Salamandar/StrangerFamily/pyStranger/database.py

#!/bin/env python3
import os
from pathlib import Path

import random
import yaml

class Sentence(object):
    def __init__(self, text, speed):
        self.text = text
        self.speed= speed

    def __repr__(self):
        return '\'' + self.text + '\''

    def __str__(self):
        return self.text


class StrangerDatabase():
    def __init__(self):
        super(StrangerDatabase, self).__init__()
        self.persistentFile = Path(os.path.dirname(__file__)+'/stranger_strings.yaml')
        self.temporaryFile  = Path(os.path.dirname(__file__)+'/stranger_strings_temp.txt')

        self.sentences      = []
        self.sentences_temp = []
        self.should_echo_last_temp = False

        self.loadPersistent()
        self.loadTemp()

    def loadPersistent(self):
        self.sentences      = self.loadFile(self.persistentFile)
    def loadTemp(self):
        self.sentences_temp = self.loadFile(self.temporaryFile)

    def loadFile(self, path):
        if not path.exists():
            return []

        with path.open() as stream:
            try:
                data = yaml.load(stream)
                return [ Sentence(d['text'], d['speed']) for d in data['sentences'] ]
            except yaml.YAMLError as exc:
                print(exc)

    def saveToTemp(self, string):
        if not os.path.isfile(str(self.temporaryFile)):
            with open(str(self.temporaryFile), 'a') as tempFile:
                tempFile.write('sentences:\n')

        with open(str(self.temporaryFile), 'a') as tempFile:
            tempFile.write('  - text: \'' + string + '\'\n')
            tempFile.write('    speed: 1\n')


    def addSentence(self, string):
        self.sentences_temp += [ Sentence(string, 1) ]
        self.should_echo_last_temp = True
        self.saveToTemp(string)


    def getRandSentence(self):
        if self.should_echo_last_temp:
            self.should_echo_last_temp = False
            return self.sentences_temp[-1]

        else:
            firstLen = len(self.sentences)
            # Check if no sentences are available
            if firstLen + len(self.sentences_temp) == 0:
                return Sentence('', 1)

            id = random.randint(0, firstLen + len(self.sentences_temp) - 1)
            if id < firstLen:
                return self.sentences[id]
            else:
                return self.sentences_temp[id - firstLen]

    def sentencesCount(self):
        return len(self.sentences) + len(self.sentences_temp)

if __name__ == '__main__':
    db = StrangerDatabase()
    db.addSentence('This is a new sentence')
    # print(db.getRandSentence())
    # print(db.getRandSentence())
    db.saveTemp()
